danjperron/blueGyro.X/catapult/DSC03209.JPG

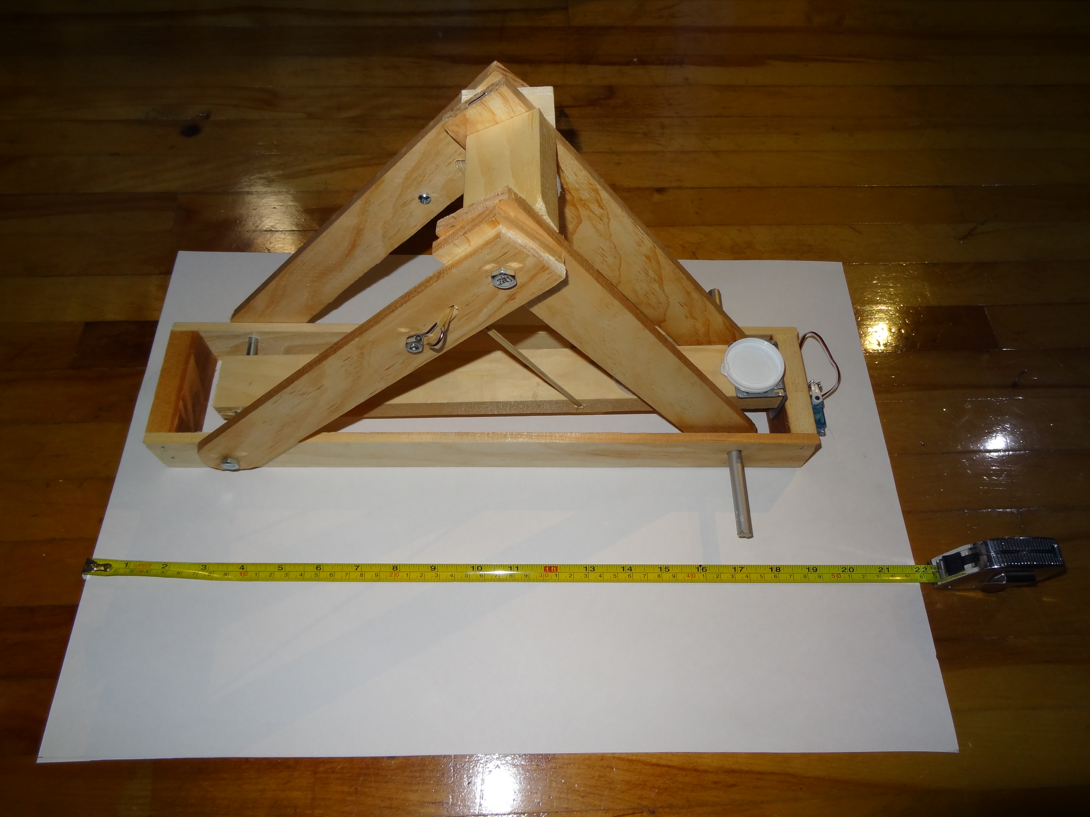
catapult/DSC03209.JPG
