danjperron/blueGyro.X/catapult/DSC03210.JPG

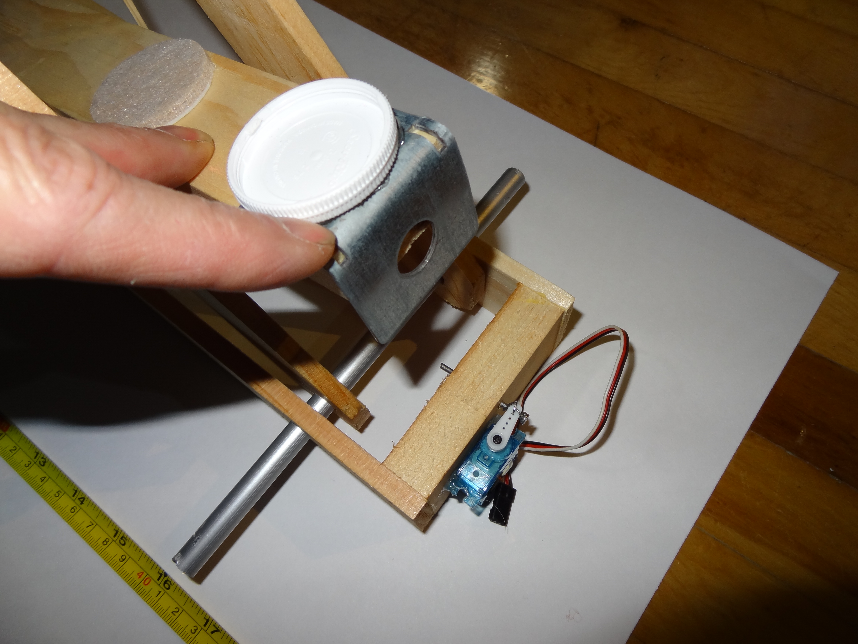
catapult/DSC03210.JPG
