danjperron/blueGyro.X/catapult/DSC03211.JPG

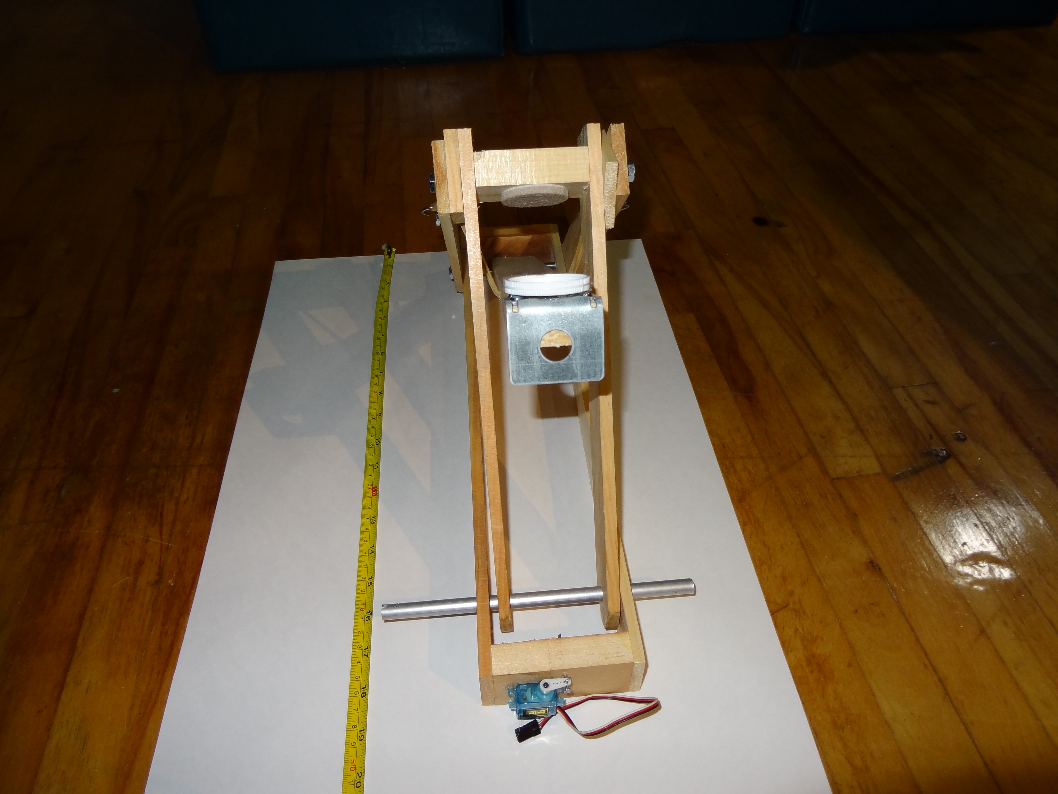
catapult/DSC03211.JPG
