danjperron/blueGyro.X/i2cMaster.c

#include <htc.h>
#include <stddef.h>
#include <conio.h>
#include <stdlib.h>
#include "i2cMaster.h"


// info extract from
// http://www.hobbytronics.co.uk/hi-tech-c-i2c-master

// Initialise MSSP port. (12F1822 - other devices may differ)
void i2c_Init(void){

   // Initialise I2C MSSP
   // Master 400KHz
   TRISA1=1;                    // set SCL and SDA pins as inputs
   TRISA2=1;

   SSPCON1 = 0b00101000; 	// I2C enabled, Master mode
   SSPCON2 = 0x00;
   // I2C Master mode, clock = FOSC/(4 * (SSPADD + 1)) 
   SSPADD = 19;    		// 400Khz @ 32Mhz Fosc

   SSPSTAT = 0b11000000; 	// Slew rate disabled

}

// i2c_Wait - wait for I2C transfer to finish
void i2c_Wait(void){
    while ( ( SSP1CON2 & 0x1F ) || ( SSPSTAT & 0x04 ) );
}

// i2c_Start - Start I2C communication
void i2c_Start(void)
{
    i2c_Wait();
    SEN=1;
}

// i2c_Restart - Re-Start I2C communication
void i2c_Restart(void){
    i2c_Wait();
    RSEN=1;
}


// i2c_Stop - Stop I2C communication
void i2c_Stop(void)
{
    i2c_Wait();
    PEN=1;
}

// i2c_Write - Sends one byte of data
void i2c_Write(unsigned char data)
{
    i2c_Wait();
    SSPBUF = data;
}

// i2c_Address - Sends Slave Address and Read/Write mode
// mode is either I2C_WRITE or I2C_READ
void i2c_Address(unsigned char address, unsigned char mode)
{
    unsigned char l_address;

    l_address=address<<1;
    l_address+=mode;
    i2c_Wait();
    SSPBUF = l_address;
}

// i2c_Read - Reads a byte from Slave device
unsigned char i2c_Read(unsigned char ack)
{
    // Read data from slave
    // ack should be 1 if there is going to be more data read
    // ack should be 0 if this is the last byte of data read
    unsigned char i2cReadData;

    i2c_Wait();
    RCEN=1;
    i2c_Wait();
    i2cReadData = SSPBUF;
    i2c_Wait();
    if ( ack ) ACKDT=0;	        // Ack
    else       ACKDT=1;	        // NAck
    ACKEN=1;                    // send acknowledge sequence

    return( i2cReadData );
}


/*********************************************************************
* Function:        LDSingleByteWriteI2C()
* Input:		Control Byte, 8 - bit address, data.
* Overview:		Write a byte to low density device at address LowAdd
********************************************************************/

void LDByteSetAddress(unsigned char i2cSlaveAddress, unsigned char LowAdd)
{
    i2c_Start();					//Generate Start COndition
    i2c_Address(i2cSlaveAddress,I2C_WRITE);
    i2c_Write(LowAdd);	                // Servo Speed 
}

void LDByteWriteI2C(unsigned char i2cSlaveAddress, unsigned char LowAdd, unsigned char data)
{
	unsigned int ErrorCode=0;
    LDByteSetAddress(i2cSlaveAddress,LowAdd);
     i2c_Write(data);	                // 2 seconds on servo 0
    i2c_Stop();	                        // send Stop
}



/*********************************************************************
* Function:        LDByteReadI2C()
* Input:		Control Byte, Address, *Data, Length.
* Overview:		Performs a low density read of Length bytes and stores in *Data array
*				starting at Address.
********************************************************************/
void LDByteReadI2C(unsigned char i2cSlaveAddress, unsigned char Address, unsigned char *Data, unsigned char Length)
{
    LDByteSetAddress(i2cSlaveAddress,Address);
    i2c_Restart();                      // Restart
    i2c_Address(i2cSlaveAddress, I2C_READ);   // Send slave address - read operation	

    while(Length-- > 1)
    *(Data++) = i2c_Read(1);            // Read one byte
    *(Data++) = i2c_Read(0);
    i2c_Stop();
}

/*
unsigned char  LDSingleByteReadI2C(unsigned char i2cSlaveAddress, unsigned char Address)
{
    unsigned char _ctemp;
    i2c_Start();
    i2c_Address(i2cSlaveAddress, I2C_WRITE);  // Send slave address - write operation
    i2c_Write(Address);	                // Set register for servo 0
    i2c_Restart();                      // Restart
    i2c_Address(i2cSlaveAddress, I2C_READ);   // Send slave address - read operation	
    _ctemp=i2c_Read(0);
    i2c_Stop();
    return(_ctemp);    
}
*/

void LDRAMSetAddress(unsigned char i2cSlaveAddress, unsigned char HighAddress, unsigned char LowAddress)
{
    i2c_Start();
    i2c_Address(i2cSlaveAddress,I2C_WRITE);
    i2c_Write(HighAddress);
    i2c_Write(LowAddress);
}

void LDRAMWriteI2C(unsigned char i2cSlaveAddress, unsigned char HighAddress, unsigned char LowAddress, unsigned char *Data, unsigned char Length)
{
    LDRAMSetAddress(i2cSlaveAddress, HighAddress,LowAddress);
    while(Length-- >0)
        i2c_Write(*(Data++));
    i2c_Stop();
}

void LDRAMReadI2C(unsigned char i2cSlaveAddress, unsigned char HighAddress, unsigned char LowAddress, unsigned char *Data, unsigned char Length)
{
    LDRAMSetAddress(i2cSlaveAddress, HighAddress,LowAddress);
    i2c_Restart();                      // Restart
    i2c_Address(i2cSlaveAddress, I2C_READ);   // Send slave address - read operation	
    while(Length-- > 1)
    *(Data++) = i2c_Read(1);            // Read one byte
    *(Data++) = i2c_Read(0);
    i2c_Stop();
}
